GuyOnWifi/fallout/docs/img/screenshots/menu.png

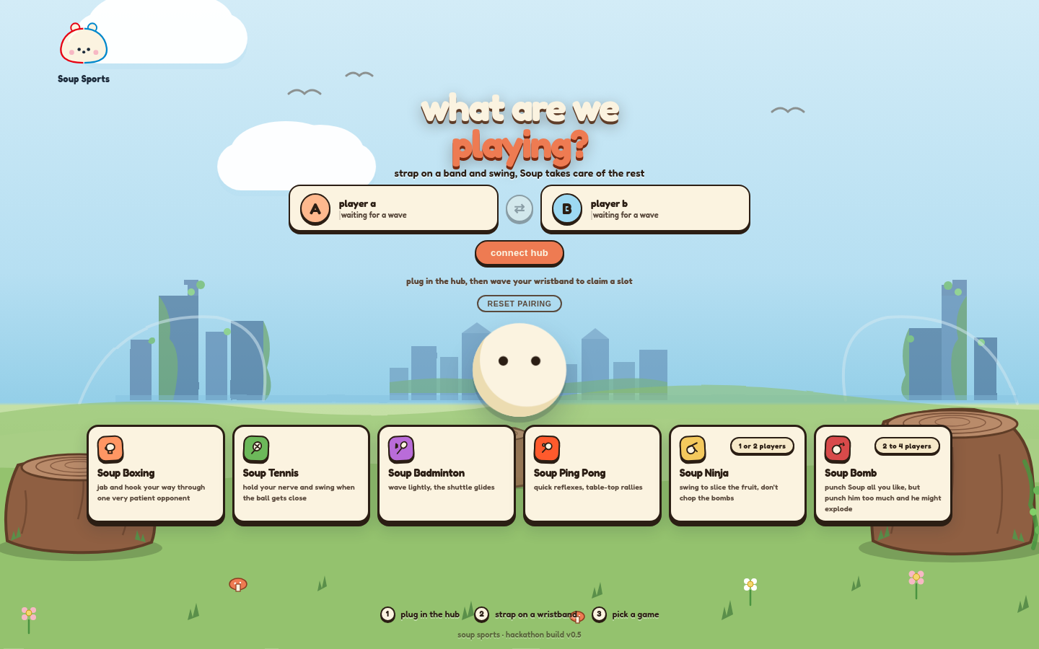
docs/img/screenshots/menu.png
