GuyOnWifi/fallout/docs/img/screenshots/slugger.png

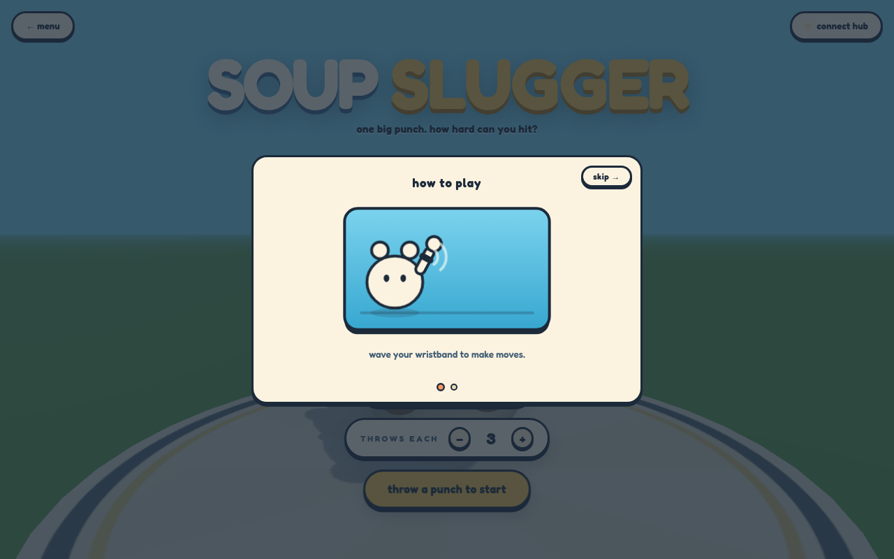
docs/img/screenshots/slugger.png
