GuyOnWifi/fallout/singleplayer/_screens_after/baseball.png

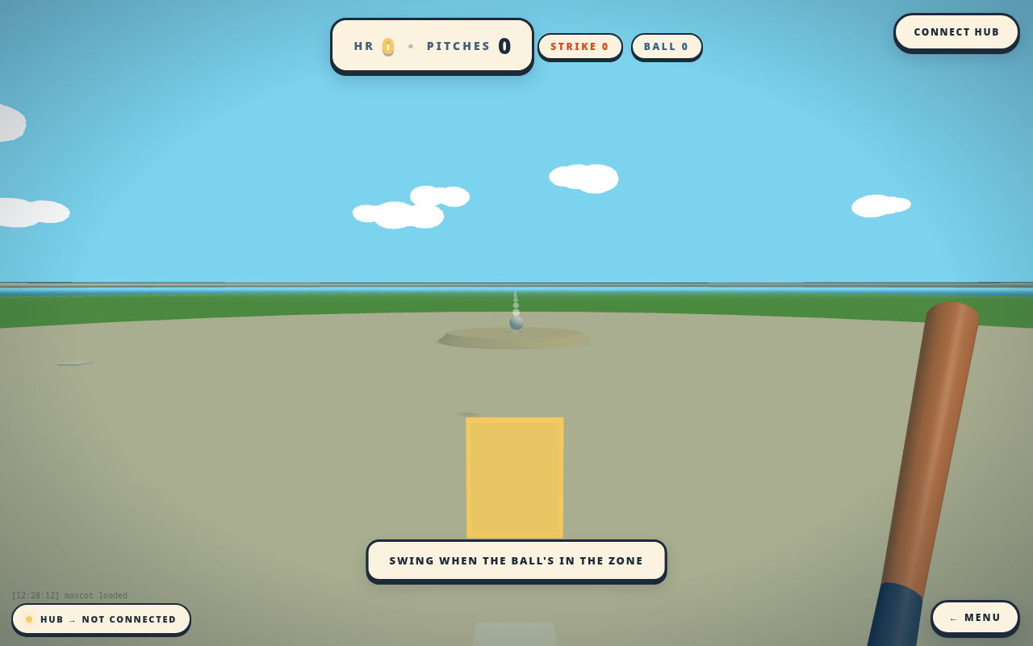
singleplayer/_screens_after/baseball.png
