GuyOnWifi/fallout/singleplayer/_screens_after/bowling.png

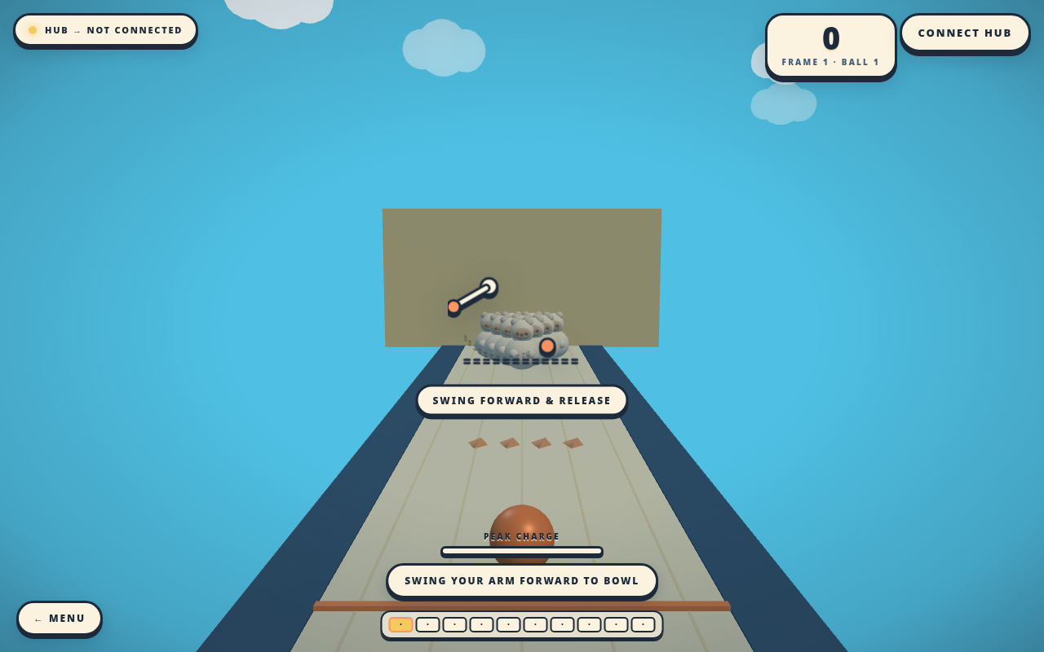
singleplayer/_screens_after/bowling.png
