GuyOnWifi/fallout/singleplayer/_screens_after/boxing.png

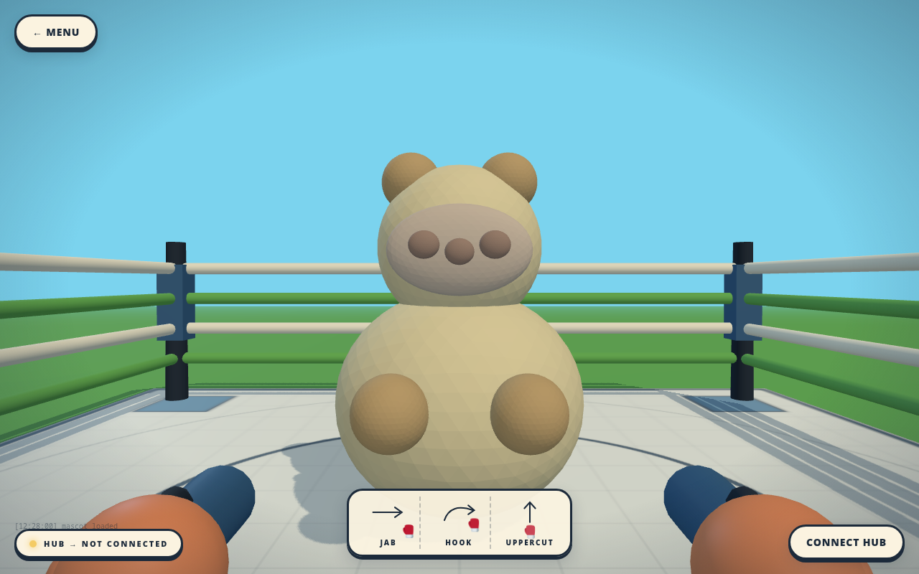
singleplayer/_screens_after/boxing.png
