GuyOnWifi/fallout/singleplayer/_screens_after/index.png

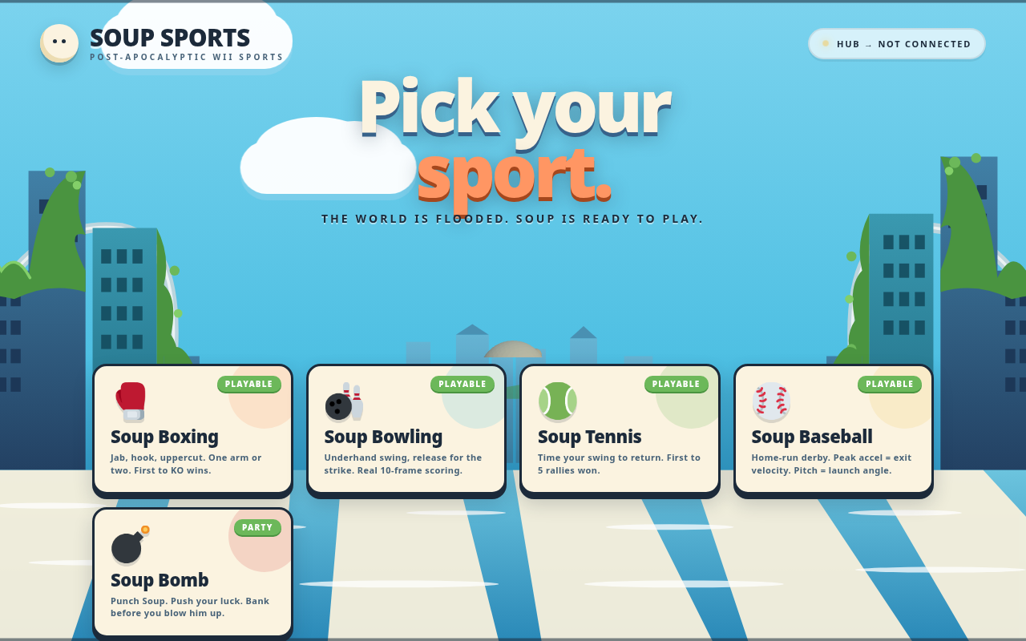
singleplayer/_screens_after/index.png
