GuyOnWifi/fallout/singleplayer/_screens_after/punch_bomb.png

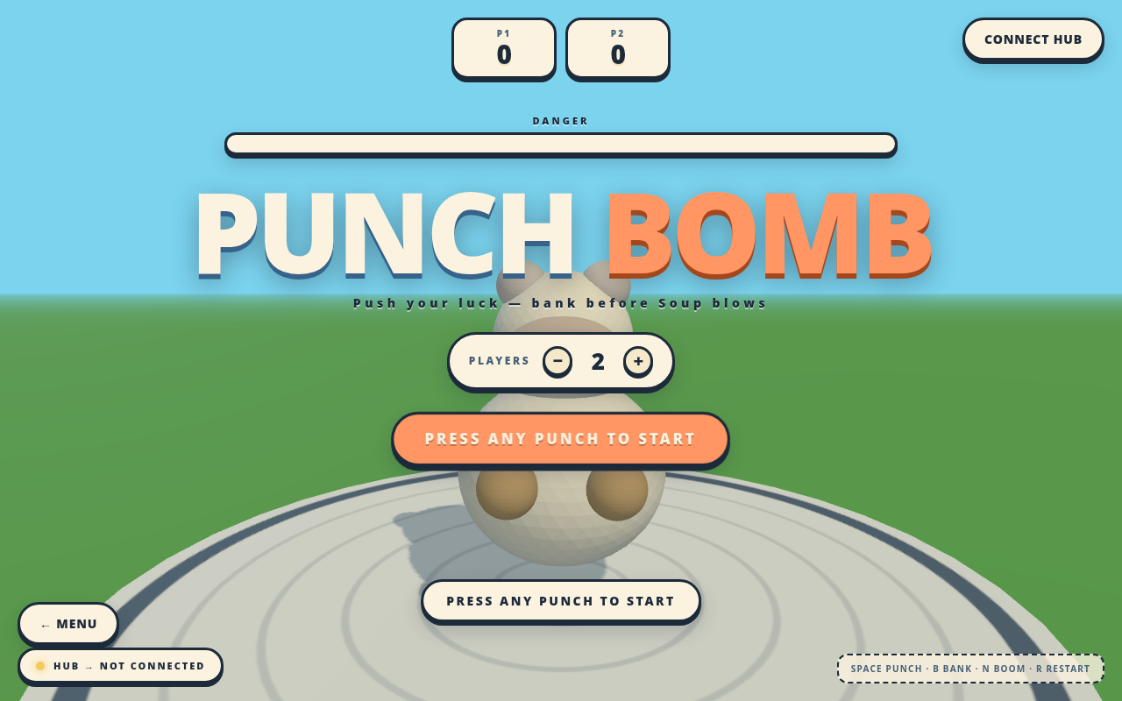
singleplayer/_screens_after/punch_bomb.png
