GuyOnWifi/fallout/singleplayer/_screens_after/punch_bomb_boom.png

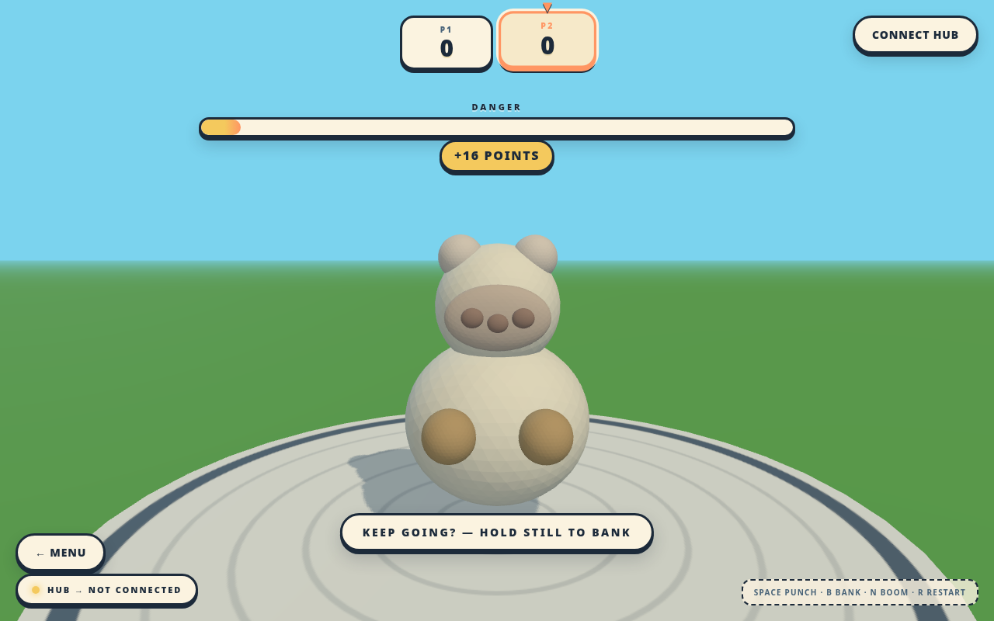
singleplayer/_screens_after/punch_bomb_boom.png
