GuyOnWifi/fallout/singleplayer/_screens_after/tennis.png

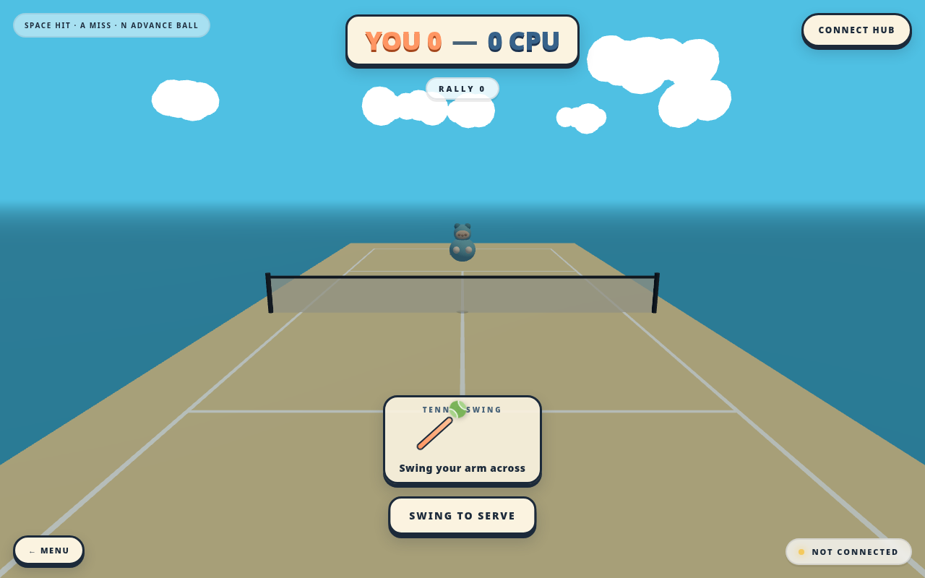
singleplayer/_screens_after/tennis.png
