GuyOnWifi/fallout/singleplayer/_screens_after_fable/baseball-desktop.png

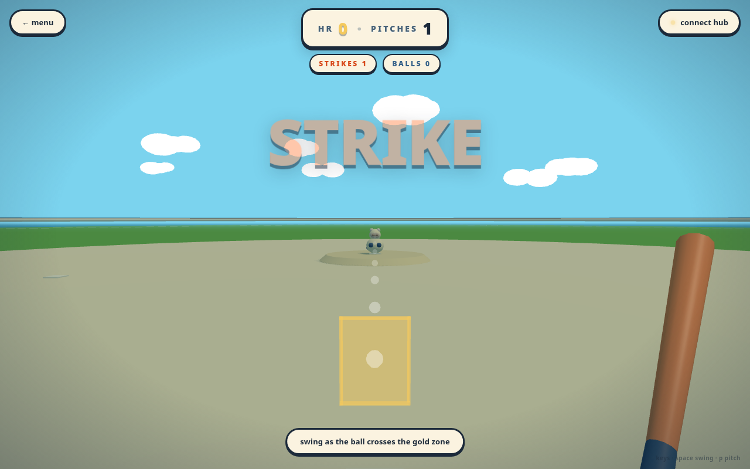
singleplayer/_screens_after_fable/baseball-desktop.png
