GuyOnWifi/fallout/singleplayer/_screens_after_fable/baseball-phone.png

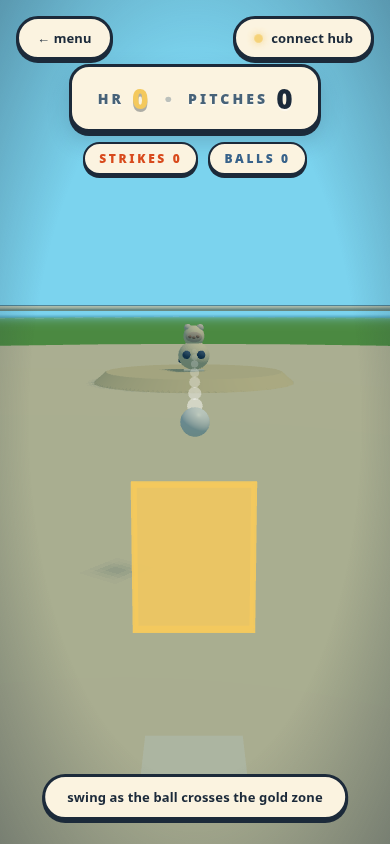
singleplayer/_screens_after_fable/baseball-phone.png
