GuyOnWifi/fallout/singleplayer/_screens_after_fable/bowling-desktop.png

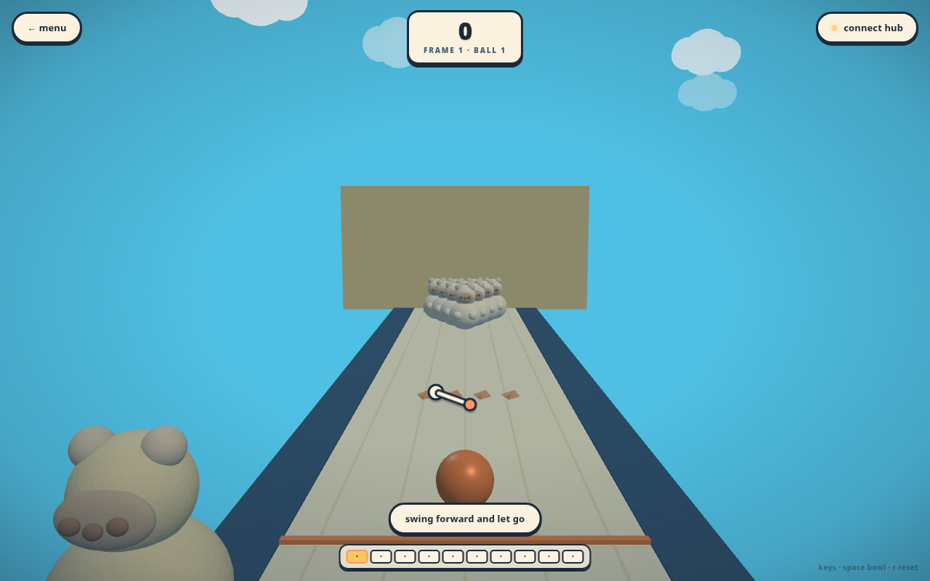
singleplayer/_screens_after_fable/bowling-desktop.png
