GuyOnWifi/fallout/singleplayer/_screens_after_fable/bowling-phone.png

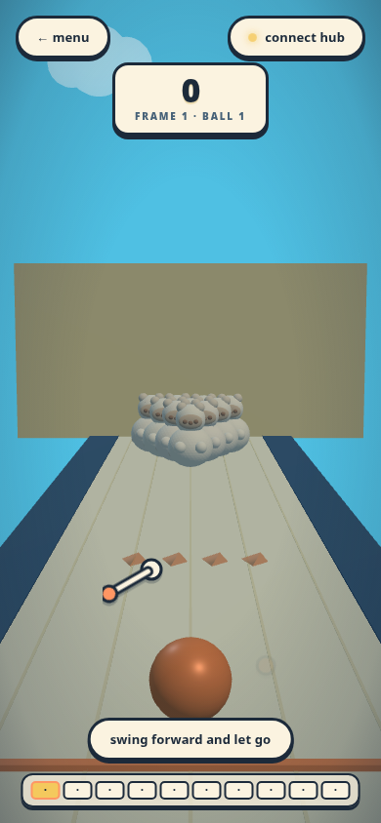
singleplayer/_screens_after_fable/bowling-phone.png
