GuyOnWifi/fallout/singleplayer/_screens_after_fable/boxing-ingame-desktop.png

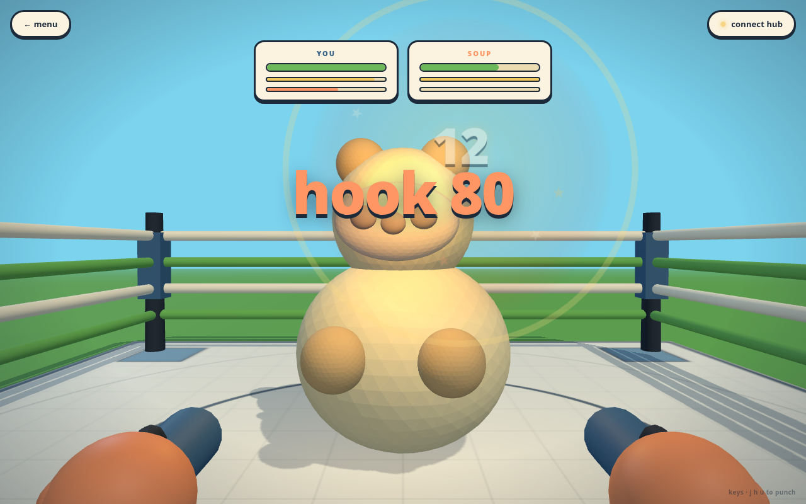
singleplayer/_screens_after_fable/boxing-ingame-desktop.png
