GuyOnWifi/fallout/singleplayer/_screens_after_fable/boxing-ingame-phone.png

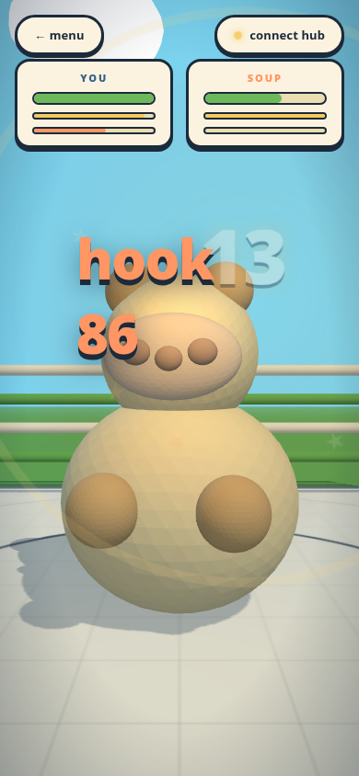
singleplayer/_screens_after_fable/boxing-ingame-phone.png
