GuyOnWifi/fallout/singleplayer/_screens_after_fable/boxing-phone.png

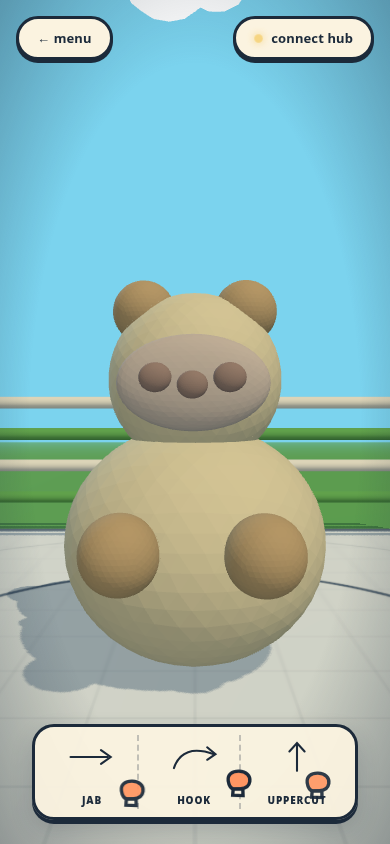
singleplayer/_screens_after_fable/boxing-phone.png
