GuyOnWifi/fallout/singleplayer/_screens_after_fable/index-desktop.png

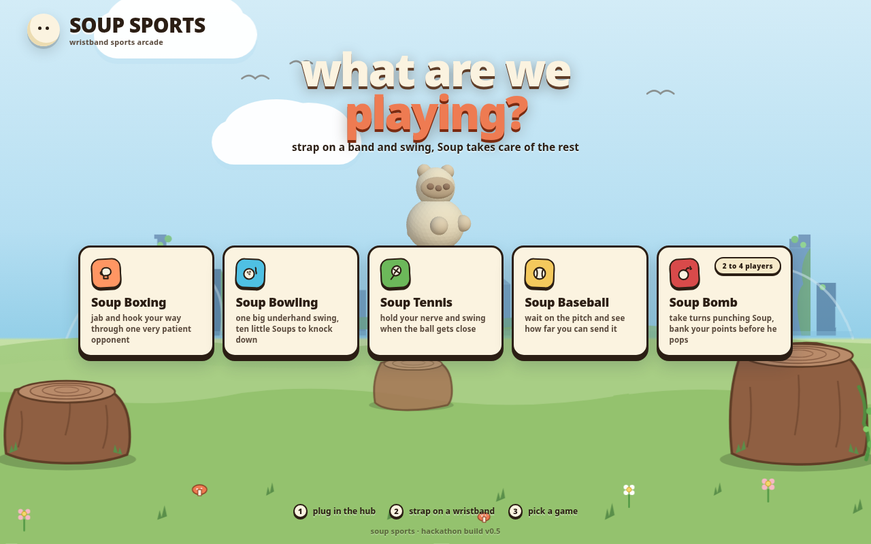
singleplayer/_screens_after_fable/index-desktop.png
