GuyOnWifi/fallout/singleplayer/_screens_after_fable/index-phone.png

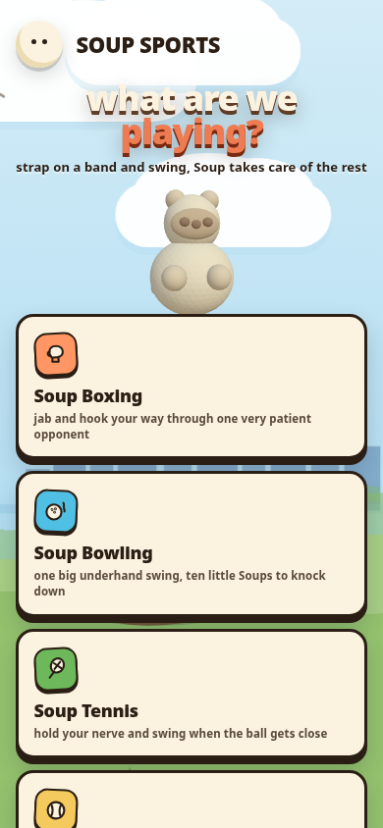
singleplayer/_screens_after_fable/index-phone.png
