GuyOnWifi/fallout/singleplayer/_screens_after_fable/punch_bomb-ingame-desktop.png

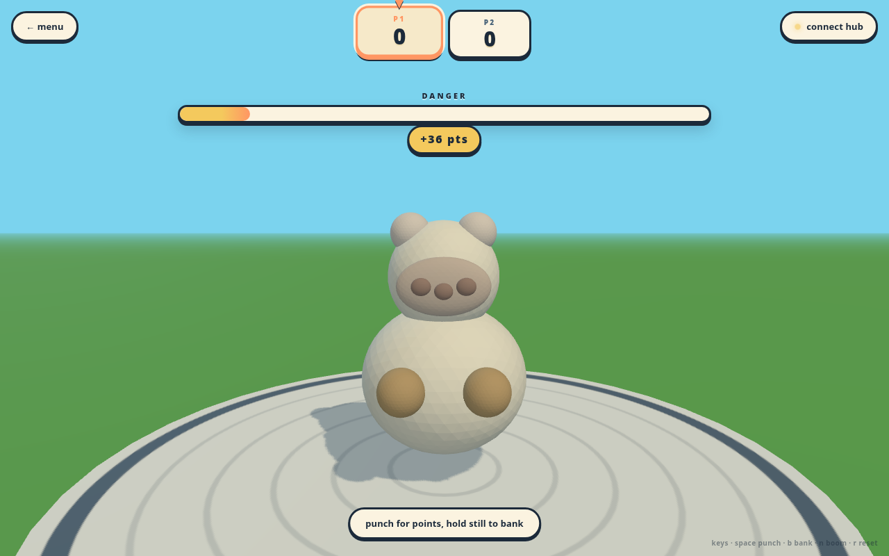
singleplayer/_screens_after_fable/punch_bomb-ingame-desktop.png
