GuyOnWifi/fallout/singleplayer/_screens_after_fable/punch_bomb-ingame-phone.png

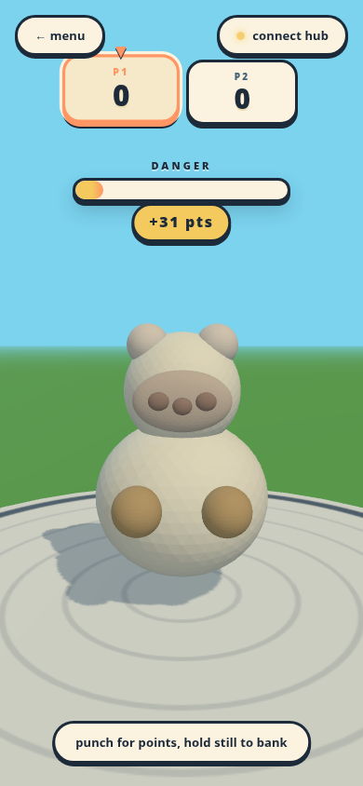
singleplayer/_screens_after_fable/punch_bomb-ingame-phone.png
