GuyOnWifi/fallout/singleplayer/_screens_after_fable/punch_bomb-phone.png

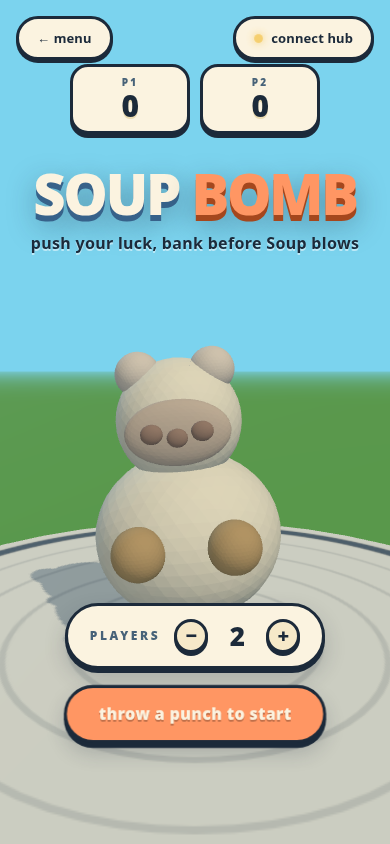
singleplayer/_screens_after_fable/punch_bomb-phone.png
