GuyOnWifi/fallout/singleplayer/_screens_after_fable/tennis-desktop.png

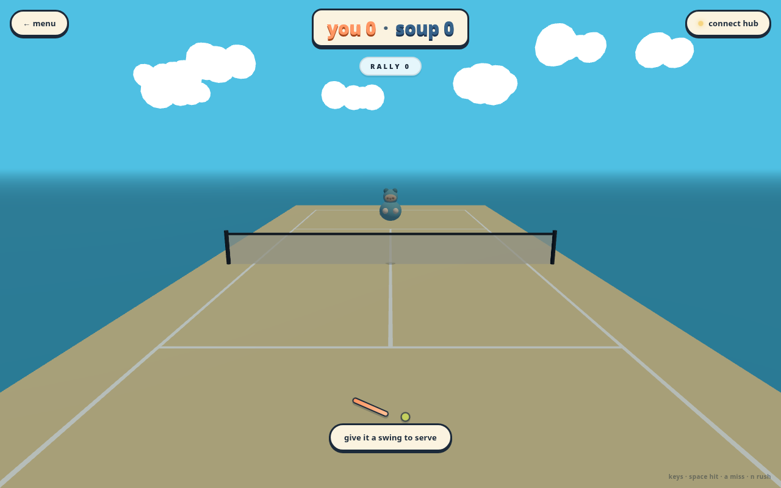
singleplayer/_screens_after_fable/tennis-desktop.png
