GuyOnWifi/fallout/singleplayer/_screens_after_fable/tennis-phone.png

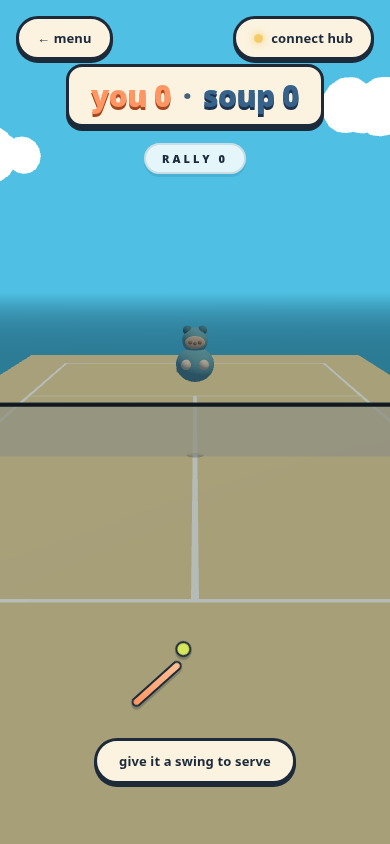
singleplayer/_screens_after_fable/tennis-phone.png
