GuyOnWifi/fallout/singleplayer/_screens_after_fable_boxing/desktop-hit-hook.png

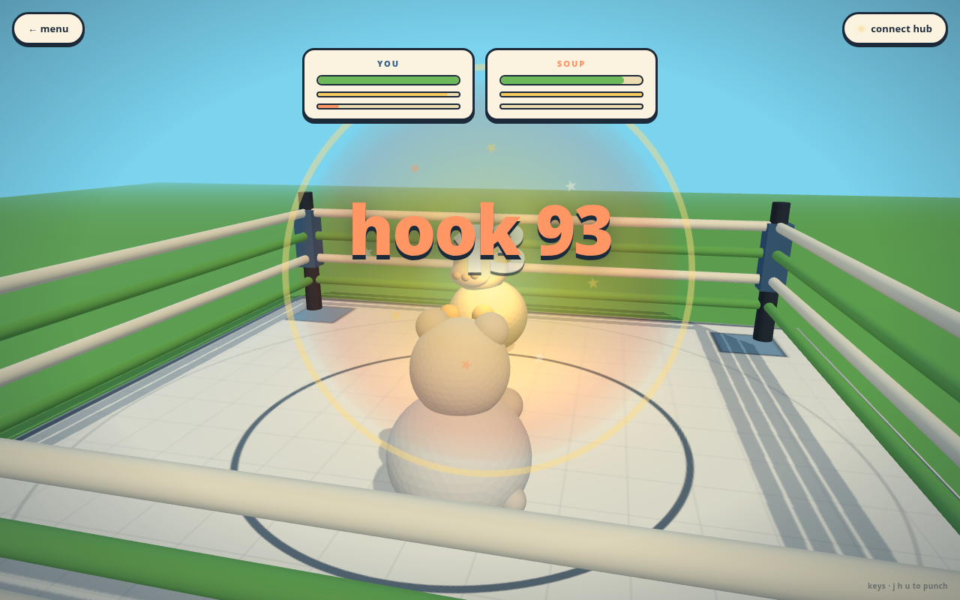
singleplayer/_screens_after_fable_boxing/desktop-hit-hook.png
