GuyOnWifi/fallout/singleplayer/_screens_after_fable_boxing/desktop-idle.png

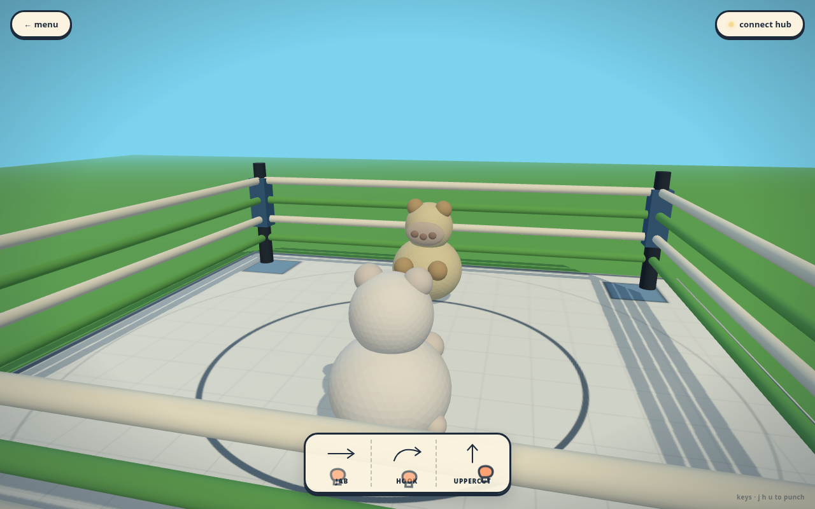
singleplayer/_screens_after_fable_boxing/desktop-idle.png
