GuyOnWifi/fallout/singleplayer/_screens_after_fable_boxing/desktop-post-ko.png

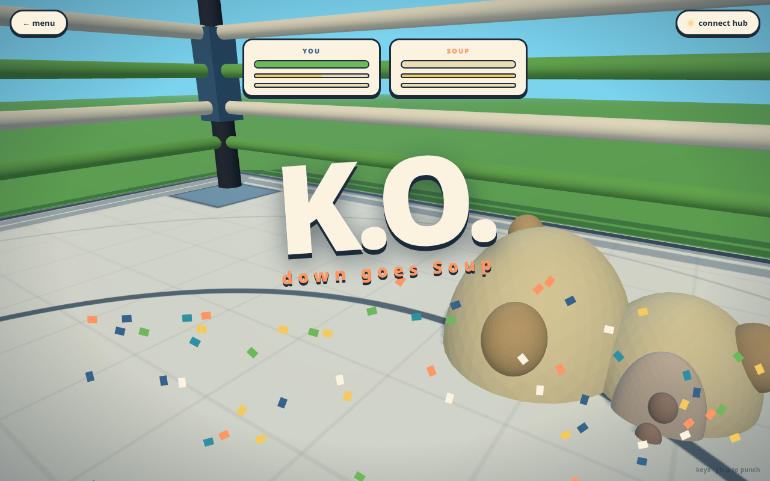
singleplayer/_screens_after_fable_boxing/desktop-post-ko.png
