GuyOnWifi/fallout/singleplayer/_screens_after_fable_boxing/phone-hit-hook.png

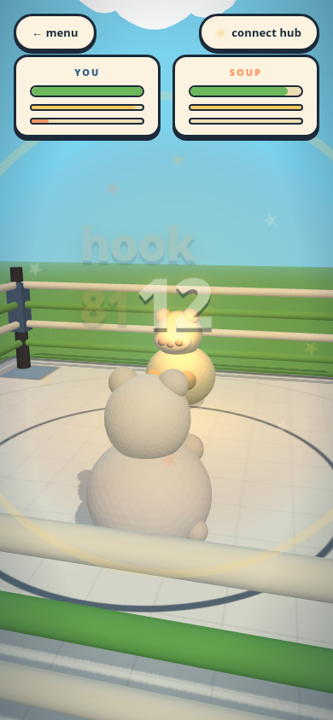
singleplayer/_screens_after_fable_boxing/phone-hit-hook.png
