GuyOnWifi/fallout/singleplayer/_screens_after_fable_boxing/phone-hit-jab.png

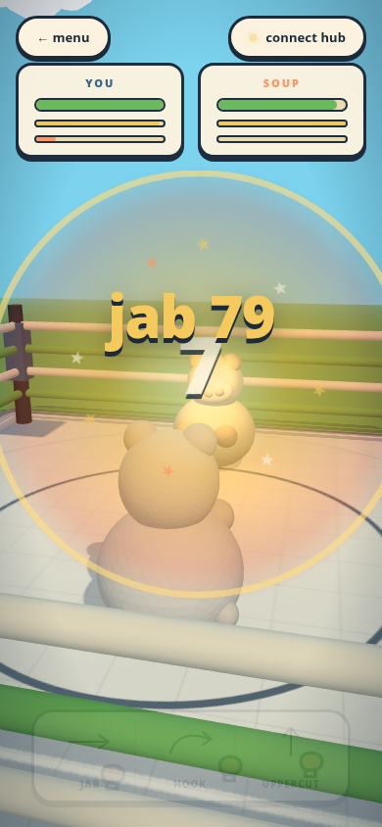
singleplayer/_screens_after_fable_boxing/phone-hit-jab.png
