GuyOnWifi/fallout/singleplayer/_screens_after_fable_boxing/phone-hit-uppercut.png

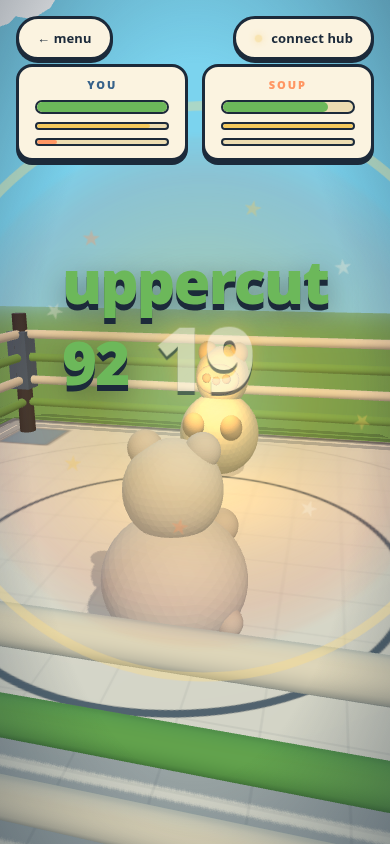
singleplayer/_screens_after_fable_boxing/phone-hit-uppercut.png
