GuyOnWifi/fallout/singleplayer/_screens_after_fable_boxing/phone-idle.png

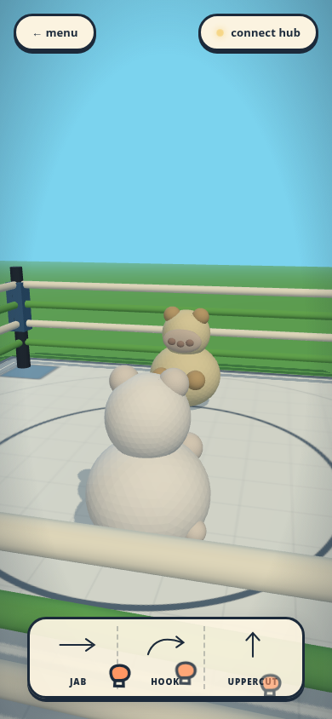
singleplayer/_screens_after_fable_boxing/phone-idle.png
