GuyOnWifi/fallout/singleplayer/_screens_after_fable_boxing/phone-mid-hook.png

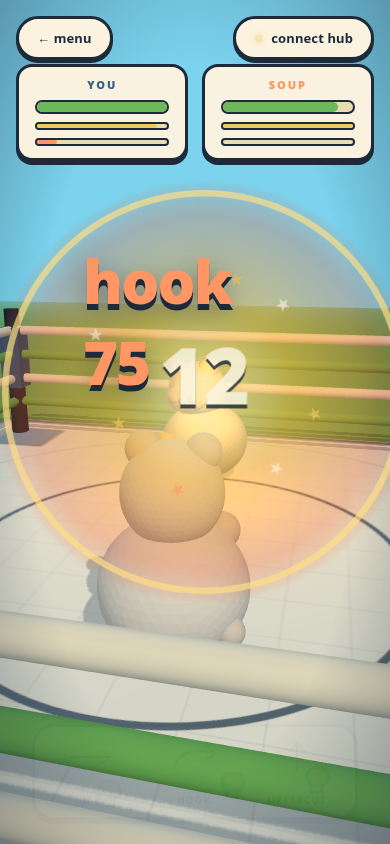
singleplayer/_screens_after_fable_boxing/phone-mid-hook.png
