GuyOnWifi/fallout/singleplayer/_screens_after_fable_boxing/phone-mid-jab.png

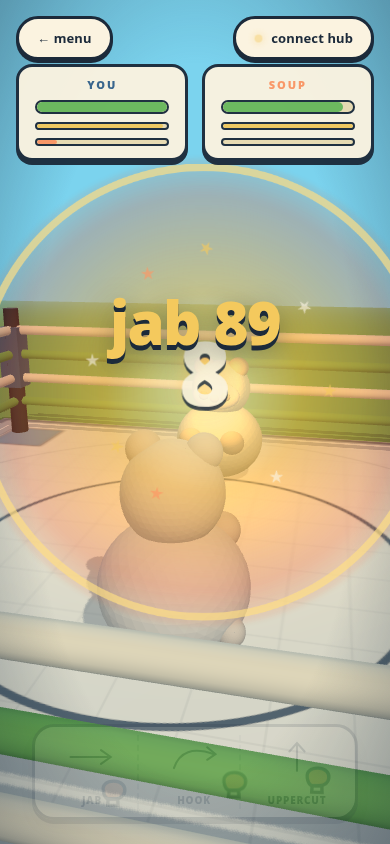
singleplayer/_screens_after_fable_boxing/phone-mid-jab.png
