GuyOnWifi/fallout/singleplayer/_screens_after_fable_boxing/phone-mid-uppercut.png

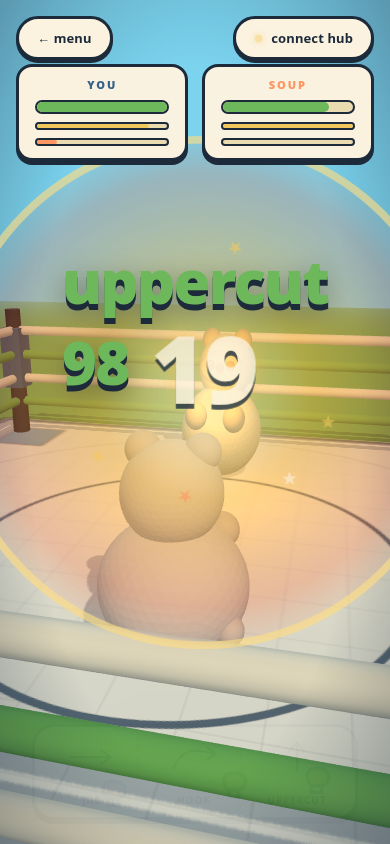
singleplayer/_screens_after_fable_boxing/phone-mid-uppercut.png
