GuyOnWifi/fallout/singleplayer/_screens_after_fable_boxing/phone-post-ko.png

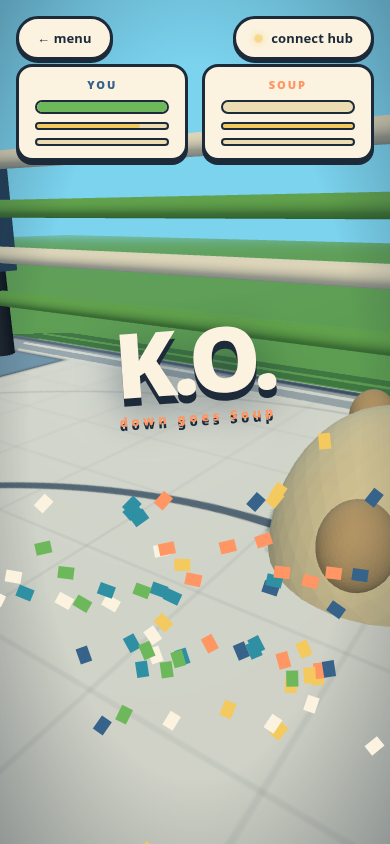
singleplayer/_screens_after_fable_boxing/phone-post-ko.png
