GuyOnWifi/fallout/singleplayer/_screens_before/baseball.png

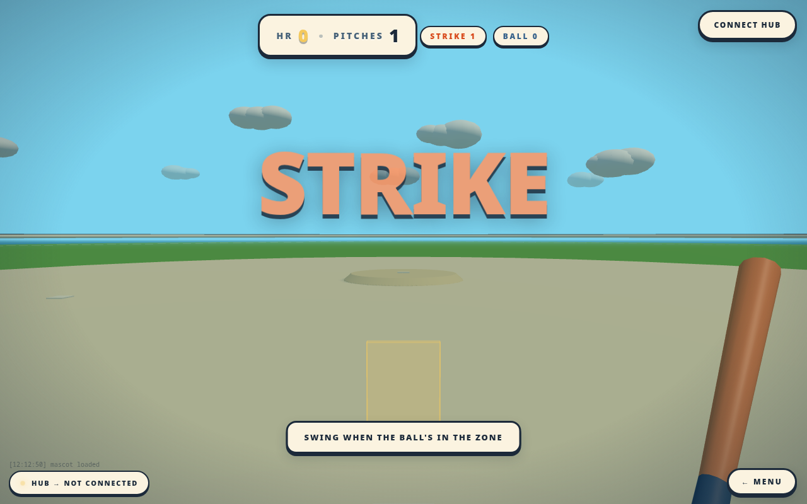
singleplayer/_screens_before/baseball.png
