GuyOnWifi/fallout/singleplayer/_screens_before/bowling.png

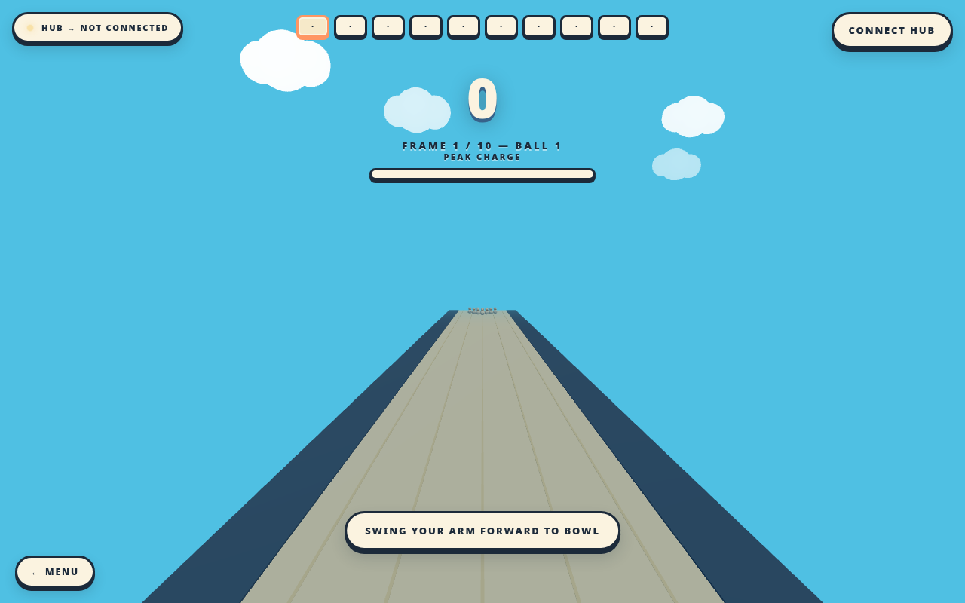
singleplayer/_screens_before/bowling.png
