GuyOnWifi/fallout/singleplayer/_screens_before/boxing.png

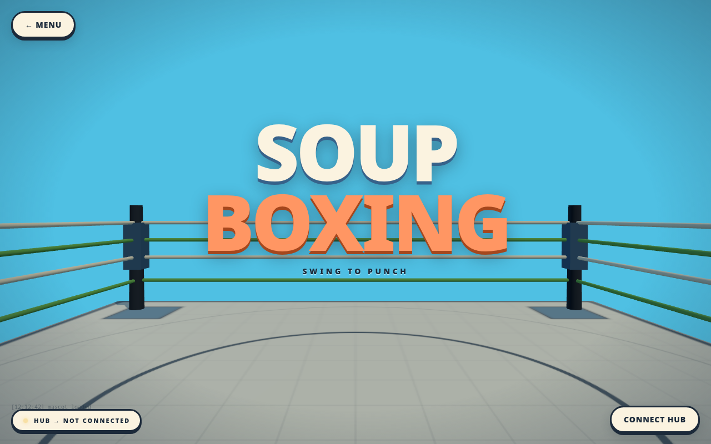
singleplayer/_screens_before/boxing.png
