GuyOnWifi/fallout/singleplayer/_screens_before/index.png

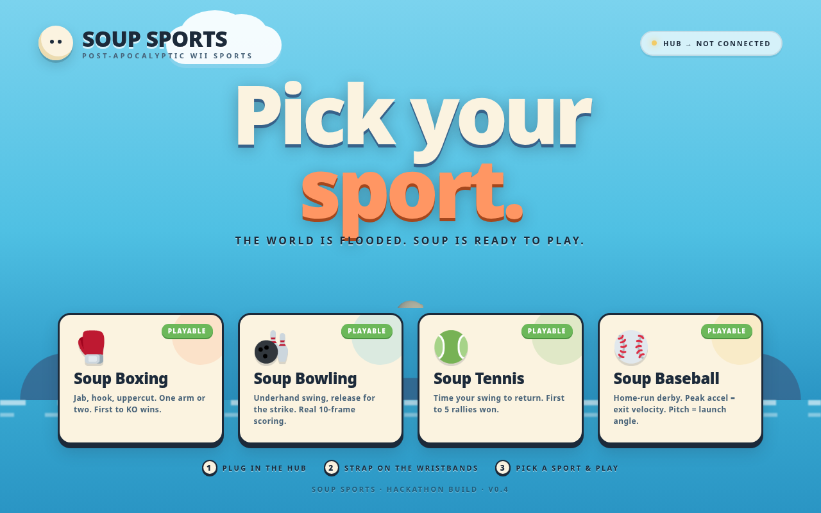
singleplayer/_screens_before/index.png
