GuyOnWifi/fallout/singleplayer/_screens_before/tennis.png

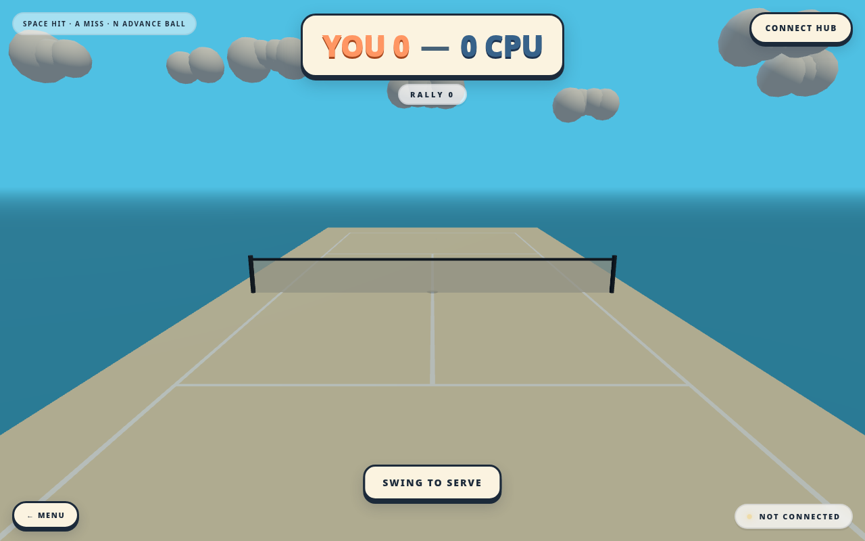
singleplayer/_screens_before/tennis.png
