GuyOnWifi/fallout/soup/refs/soup_reference_sitting.png

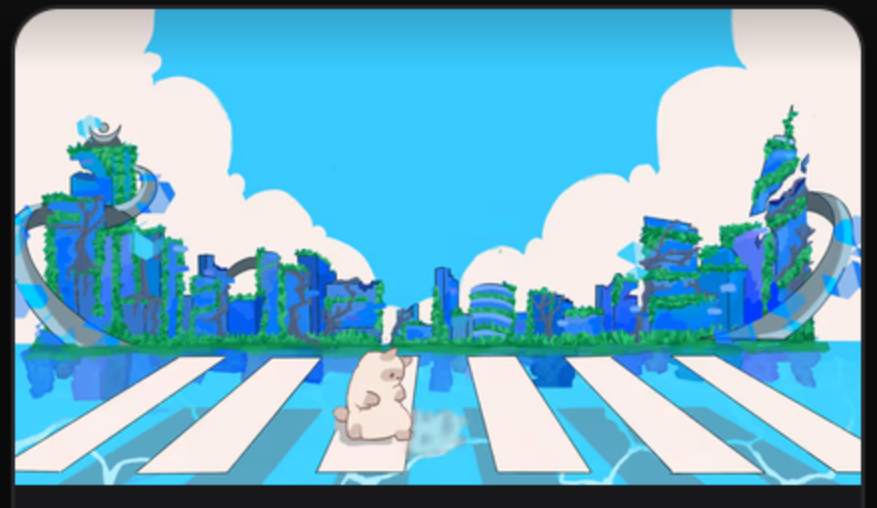
soup/refs/soup_reference_sitting.png
