GuyOnWifi/fallout/soup/soup_render.png

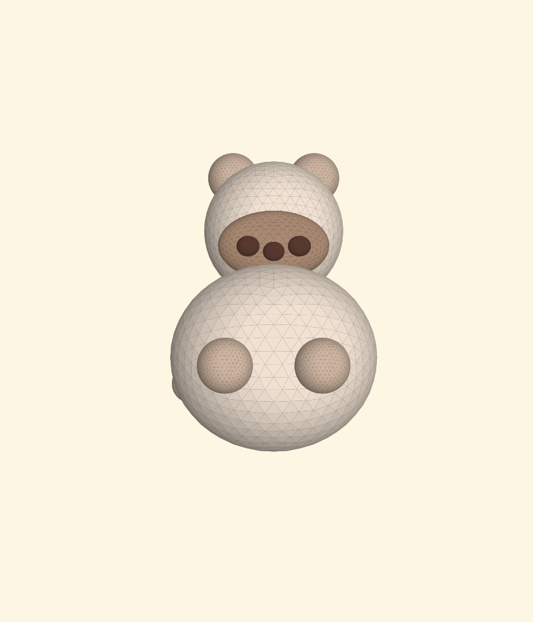
soup/soup_render.png
