GuyOnWifi/fallout/hardware/wristband.kicad_sch

## KiCad design hardware/wristband.kicad_sch (2026-07-06)

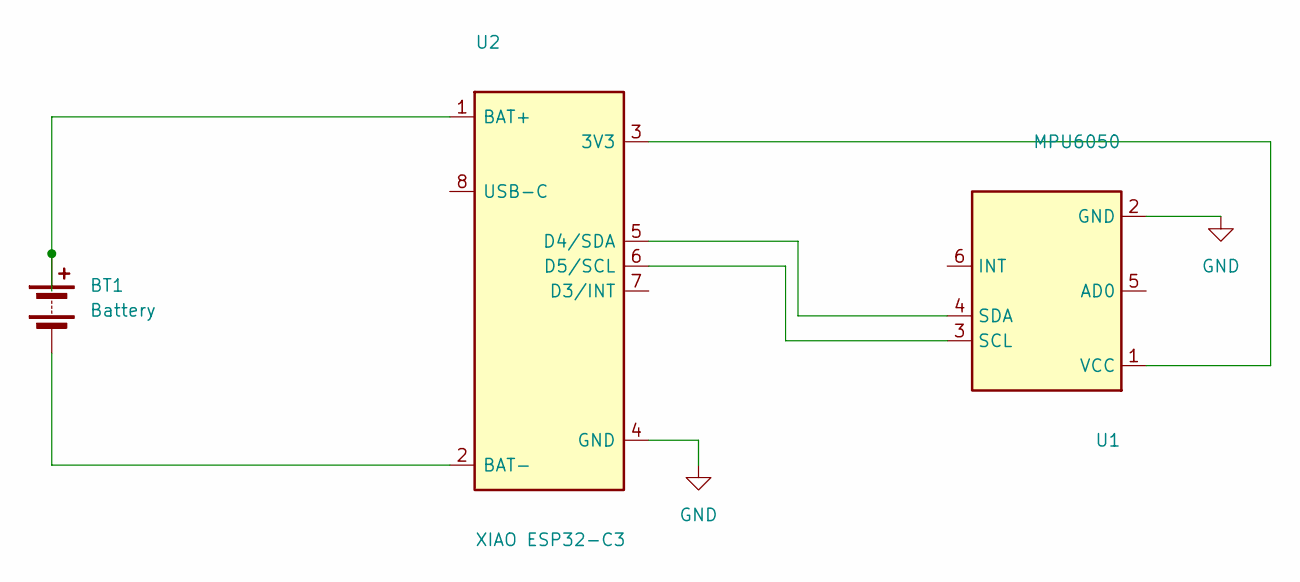
[picture p63: schematic wristband.kicad_sch]

Parts:
BT1: Battery
U1: MPU6050
U2: XIAO ESP32-C3

Connections:
GND: U1.2 (GND), U2.4 (GND)
unnamed: BT1.1 (+), U2.1 (BAT+)
unnamed: BT1.2 (-), U2.2 (BAT-)
unnamed: U1.1 (VCC), U2.3 (3V3)
unnamed: U1.3 (SCL), U2.6 (D5/SCL)
unnamed: U1.4 (SDA), U2.5 (D4/SDA)
